kdsuneraavinash/mcu-project/complete.png

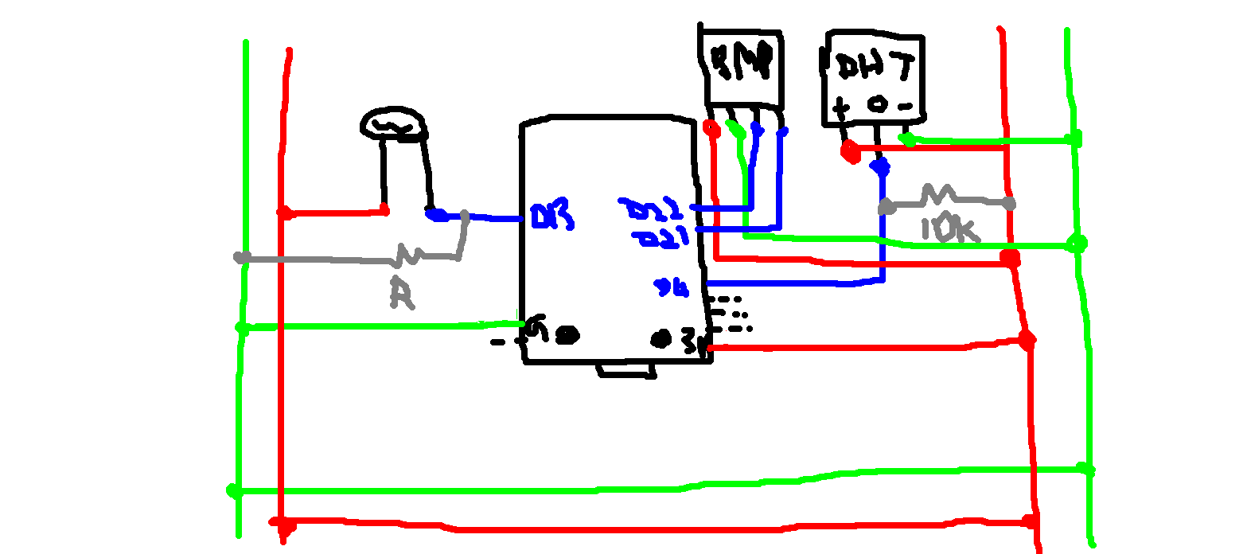
complete.png
