kdsuneraavinash/mcu-project/dht.png

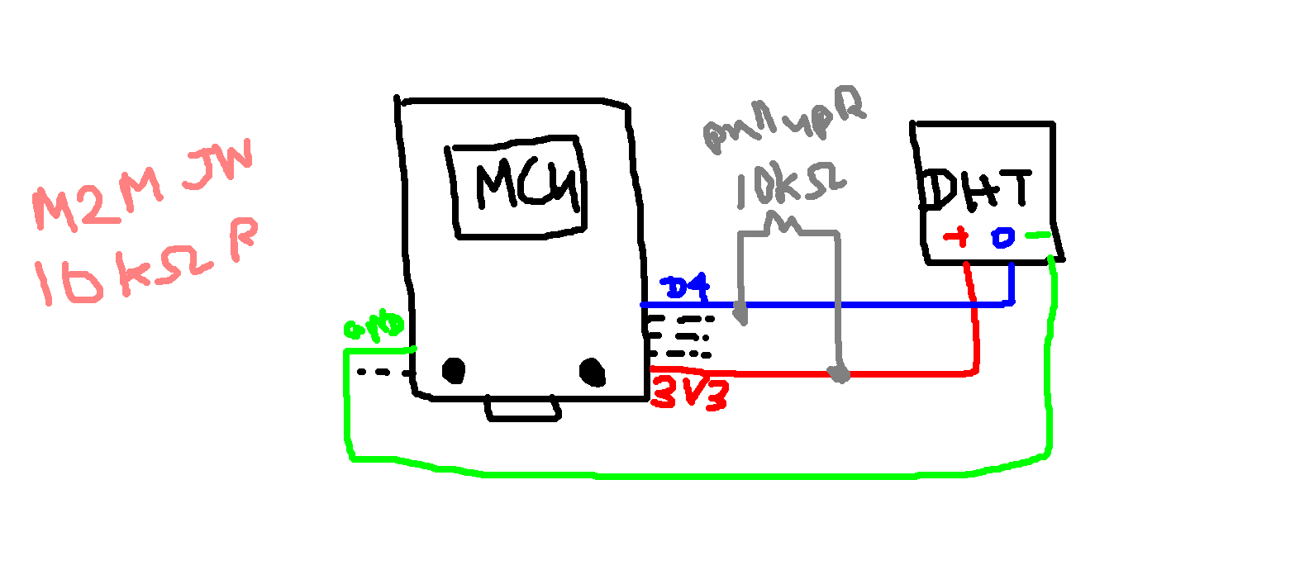
dht.png
